playlogo/Aereo/Aereo/src/sensors/pms5003.h

#ifndef PMS5003MODULE_H
#define PMS5003MODULE_H

#include <HardwareSerial.h>

struct pms5003data
{
    uint16_t framelen;
    uint16_t pm10_standard, pm25_standard, pm100_standard;
    uint16_t pm10_env, pm25_env, pm100_env;
    uint16_t particles_03um, particles_05um, particles_10um, particles_25um, particles_50um, particles_100um;
    uint16_t unused;
    uint16_t checksum;
};

bool setupPMS5003();

bool readPMSdata(Stream *s);
void loopPMS5003(void *parameter);

#endif
